Tedros00/Mouse-Pi/3D parts/SW/RaspberryPi5.SLDPRT

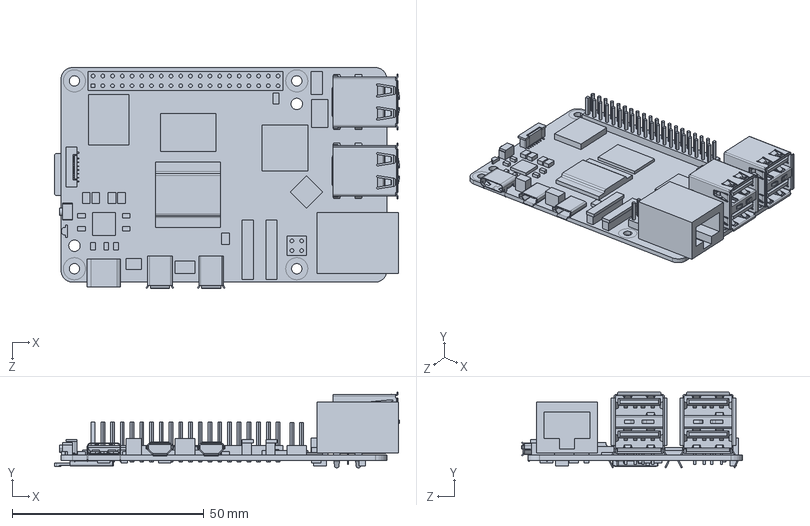
[picture p17: CAD file, 2025-12-06]
3D parts/SW/RaspberryPi5.SLDPRT
90.0 x 19.8 x 57.7 mm
