Tedros00/Mouse-Pi/3D parts/STL/LidarMount.STL

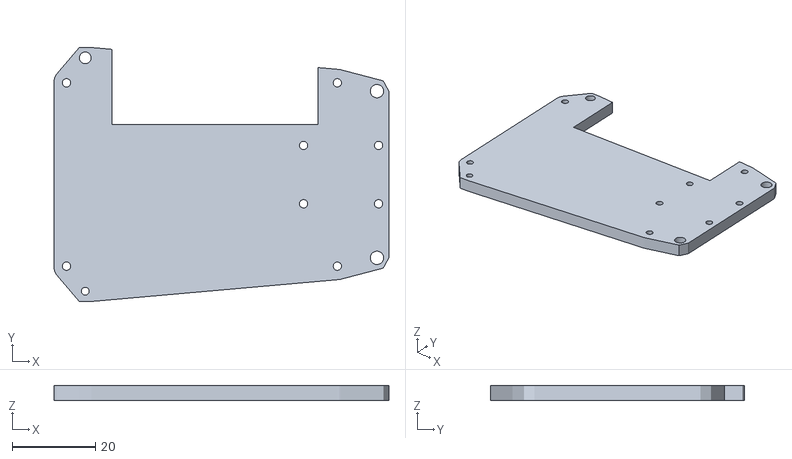
[picture p18: CAD file, 2025-12-06]
3D parts/STL/LidarMount.STL
80.4 x 61.1 x 3.50
