Tedros00/Mouse-Pi/3D parts/SW/barrel.SLDPRT

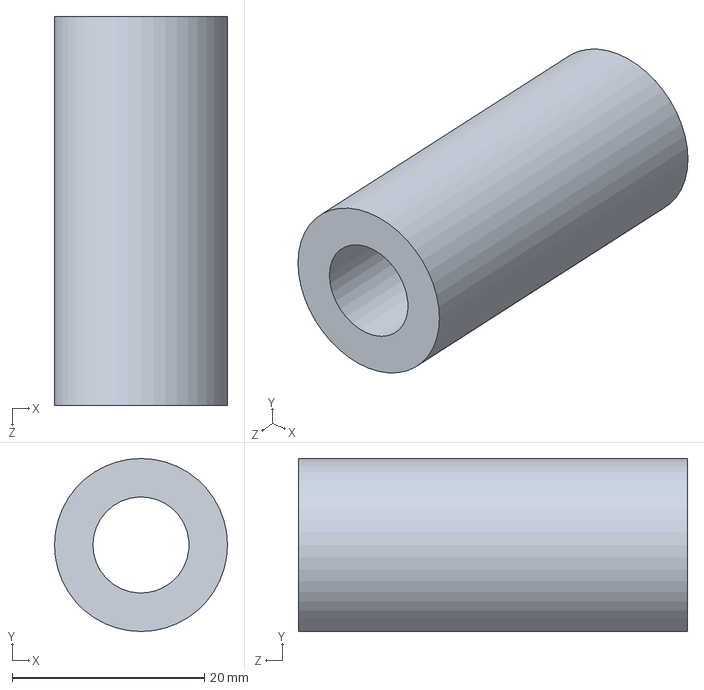
[picture p19: CAD file, 2025-12-06]
3D parts/SW/barrel.SLDPRT
18.0 x 18.0 x 40.5 mm
