Tedros00/Mouse-Pi/3D parts/mouse.SLDASM

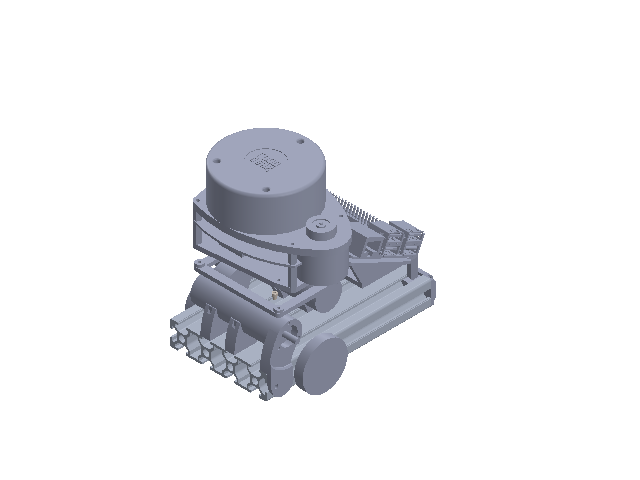
[picture p20: CAD file, 2025-12-06]
3D parts/mouse.SLDASM
2080 Extrusion
wheel x 3
barrel
Part5^mouse
Motor x 2
Part6^mouse x 2
pot
Part8^mouse x 2
Part9^mouse x 4
socket head cap screw_am
RaspberryPi5
Part66^mouse
Part67^mouse
arduino mount
Part69^mouse
rplidar_main
MirrorPart5^mouse
