Tedros00/Mouse-Pi/Gazebo/results/map.png

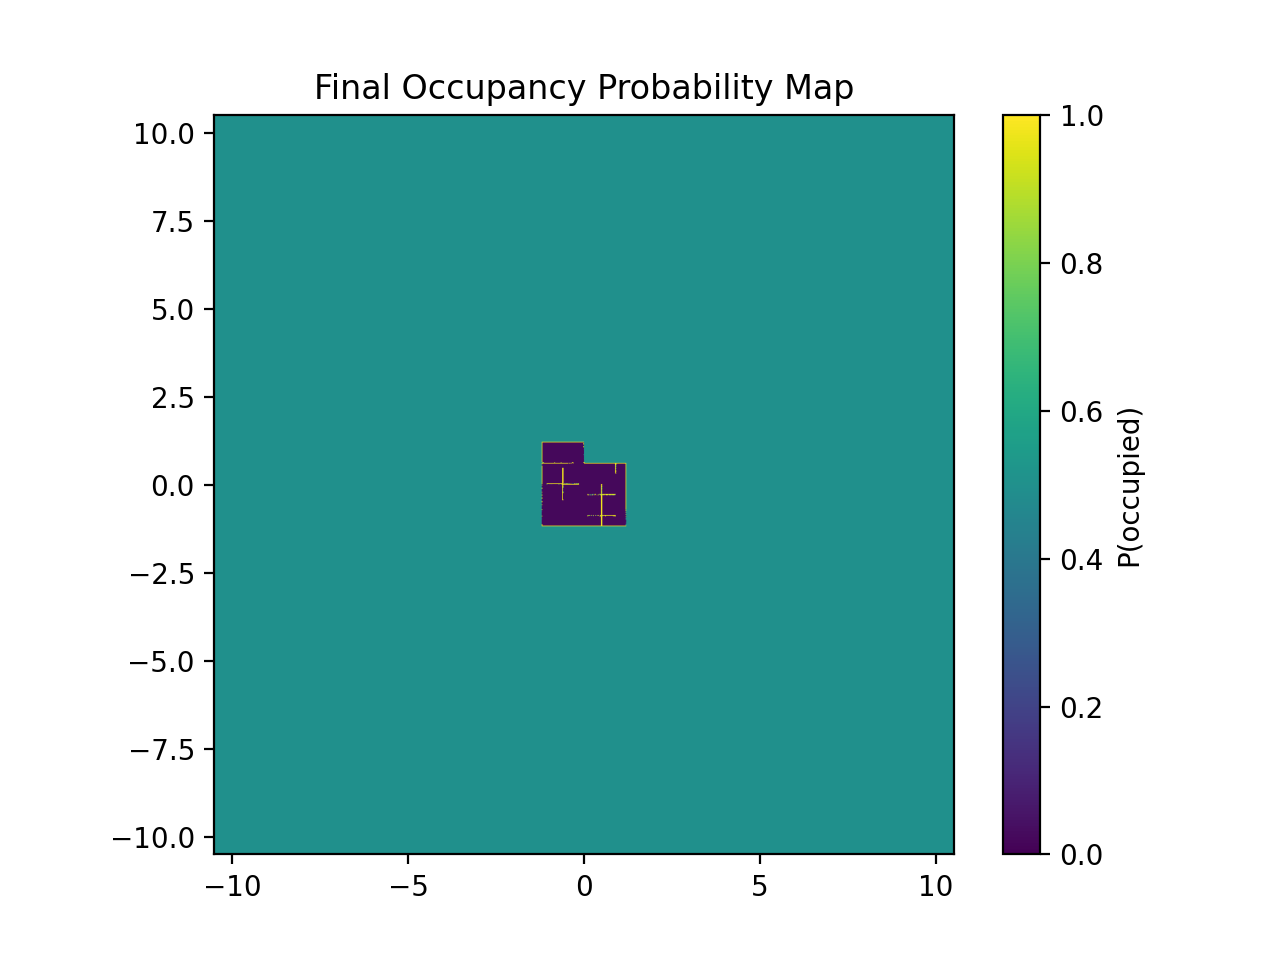
Gazebo/results/map.png
